mpb27/hp-3478a-fram/simulations/ltspice/01 - RST Line Discharge.asc

B1: bi; I={V(RST)>2.0 ? 0.150 : V(RST)*0.075}
C1: cap; 1µ
Named nets: 0, RST
.ic V(RST)=5
.tran 70u
01 - RST Line Discharge With APX803 Open-Drain FET Model
From APX803 datasheet.  With Vgs=4V, the Ids is
150mA if Vds>2V, and is linear from 0 to 150mA below 2V Vds (~13ohm).
RESULT:
Discharge time from 5V to 0.5V is ~40us.
Note that the LM339N open-drain output is likely very similar
given the 0.5Vmax @ 4mA (which is the same spec as APX803).
