mpb27/hp-3478a-fram/simulations/ltspice/02 - LM339 Input Level Without Battery.asc

D1: diode; MMSD4148
R1: res; 17.4k
R2: res; 6.5k
R3: res; 6.5k
R4: res; 200k
R5: res; 470
R6: res; 100G
U1: LM339A_TI
V1: voltage; 12
V2: voltage; 5
Named nets: 0, RST, INN, UNREGULATED_5V_REALLY_12V, REGULATED_5V, INP
02 - LM339 Input Level Without Battery (Battery Removed)
BATTERY
TERMINALS
.dc V1 11 13 0.1
RESULTS:
 
Very dependent on D1 diode and input bias current of
LM339.  INN is ~5V if floating -- while INP is between
4.8V and 5.5V (11 to 13V unregulated supply).
 
Probably want a weak pull-down on INN. Even 10-20Mohm is
enough.
